polya2005/IoT-RGB-matrix/display_driver/src/gowin_sdpb/gowin_sdpb.v

//Copyright (C)2014-2025 Gowin Semiconductor Corporation.
//All rights reserved.
//File Title: IP file
//Tool Version: V1.9.11.03 Education
//Part Number: GW1NR-LV9QN88PC6/I5
//Device: GW1NR-9
//Device Version: C
//Created Time: Wed Aug 12 21:27:03 2026

module Gowin_SDPB_320_8 (dout, clka, cea, reseta, clkb, ceb, resetb, oce, ada, din, adb);

output [7:0] dout;
input clka;
input cea;
input reseta;
input clkb;
input ceb;
input resetb;
input oce;
input [8:0] ada;
input [7:0] din;
input [8:0] adb;

wire [23:0] sdpb_inst_0_dout_w;
wire gw_gnd;

assign gw_gnd = 1'b0;

SDPB sdpb_inst_0 (
    .DO({sdpb_inst_0_dout_w[23:0],dout[7:0]}),
    .CLKA(clka),
    .CEA(cea),
    .RESETA(reseta),
    .CLKB(clkb),
    .CEB(ceb),
    .RESETB(resetb),
    .OCE(oce),
    .BLKSELA({gw_gnd,gw_gnd,gw_gnd}),
    .BLKSELB({gw_gnd,gw_gnd,gw_gnd}),
    .ADA({gw_gnd,gw_gnd,ada[8:0],gw_gnd,gw_gnd,gw_gnd}),
    .DI({gw_gnd,gw_gnd,gw_gnd,gw_gnd,gw_gnd,gw_gnd,gw_gnd,gw_gnd,gw_gnd,gw_gnd,gw_gnd,gw_gnd,gw_gnd,gw_gnd,gw_gnd,gw_gnd,gw_gnd,gw_gnd,gw_gnd,gw_gnd,gw_gnd,gw_gnd,gw_gnd,gw_gnd,din[7:0]}),
    .ADB({gw_gnd,gw_gnd,adb[8:0],gw_gnd,gw_gnd,gw_gnd})
);

defparam sdpb_inst_0.READ_MODE = 1'b0;
defparam sdpb_inst_0.BIT_WIDTH_0 = 8;
defparam sdpb_inst_0.BIT_WIDTH_1 = 8;
defparam sdpb_inst_0.BLK_SEL_0 = 3'b000;
defparam sdpb_inst_0.BLK_SEL_1 = 3'b000;
defparam sdpb_inst_0.RESET_MODE = "SYNC";

endmodule //Gowin_SDPB_320_8
