polya2005/IoT-RGB-matrix/display_driver/src/bsram_dp/bsram_dp.v

`timescale 1ns/1ps
//Copyright (C)2014-2025 Gowin Semiconductor Corporation.
//All rights reserved.
//File Title: IP file
//Tool Version: V1.9.11.03 Education
//Part Number: GW1NR-LV9QN88PC6/I5
//Device: GW1NR-9
//Device Version: C
//Created Time: Fri Jul 31 19:23:53 2026

module bsram_dp (douta, doutb, clka, ocea, cea, reseta, wrea, clkb, oceb, ceb, resetb, wreb, ada, dina, adb, dinb);

output [7:0] douta;
output [7:0] doutb;
input clka;
input ocea;
input cea;
input reseta;
input wrea;
input clkb;
input oceb;
input ceb;
input resetb;
input wreb;
input [0:0] ada;
input [7:0] dina;
input [0:0] adb;
input [7:0] dinb;

wire [7:0] dpb_inst_0_douta_w;
wire [7:0] dpb_inst_0_doutb_w;
wire gw_gnd;

assign gw_gnd = 1'b0;

DPB dpb_inst_0 (
    .DOA({dpb_inst_0_douta_w[7:0],douta[7:0]}),
    .DOB({dpb_inst_0_doutb_w[7:0],doutb[7:0]}),
    .CLKA(clka),
    .OCEA(ocea),
    .CEA(cea),
    .RESETA(reseta),
    .WREA(wrea),
    .CLKB(clkb),
    .OCEB(oceb),
    .CEB(ceb),
    .RESETB(resetb),
    .WREB(wreb),
    .BLKSELA({gw_gnd,gw_gnd,gw_gnd}),
    .BLKSELB({gw_gnd,gw_gnd,gw_gnd}),
    .ADA({gw_gnd,gw_gnd,gw_gnd,gw_gnd,gw_gnd,gw_gnd,gw_gnd,gw_gnd,gw_gnd,gw_gnd,ada[0],gw_gnd,gw_gnd,gw_gnd}),
    .DIA({gw_gnd,gw_gnd,gw_gnd,gw_gnd,gw_gnd,gw_gnd,gw_gnd,gw_gnd,dina[7:0]}),
    .ADB({gw_gnd,gw_gnd,gw_gnd,gw_gnd,gw_gnd,gw_gnd,gw_gnd,gw_gnd,gw_gnd,gw_gnd,adb[0],gw_gnd,gw_gnd,gw_gnd}),
    .DIB({gw_gnd,gw_gnd,gw_gnd,gw_gnd,gw_gnd,gw_gnd,gw_gnd,gw_gnd,dinb[7:0]})
);

defparam dpb_inst_0.READ_MODE0 = 1'b0;
defparam dpb_inst_0.READ_MODE1 = 1'b0;
defparam dpb_inst_0.WRITE_MODE0 = 2'b00;
defparam dpb_inst_0.WRITE_MODE1 = 2'b00;
defparam dpb_inst_0.BIT_WIDTH_0 = 8;
defparam dpb_inst_0.BIT_WIDTH_1 = 8;
defparam dpb_inst_0.BLK_SEL_0 = 3'b000;
defparam dpb_inst_0.BLK_SEL_1 = 3'b000;
defparam dpb_inst_0.RESET_MODE = "SYNC";

endmodule //bsram_dp
