polya2005/IoT-RGB-matrix/display_driver/src/gowin_sdpb/gowin_sdpb_tmp.v

//Copyright (C)2014-2025 Gowin Semiconductor Corporation.
//All rights reserved.
//File Title: Template file for instantiation
//Tool Version: V1.9.11.03 Education
//Part Number: GW1NR-LV9QN88PC6/I5
//Device: GW1NR-9
//Device Version: C
//Created Time: Wed Aug 12 21:27:03 2026

//Change the instance name and port connections to the signal names
//--------Copy here to design--------

    Gowin_SDPB_320_8 your_instance_name(
        .dout(dout), //output [7:0] dout
        .clka(clka), //input clka
        .cea(cea), //input cea
        .reseta(reseta), //input reseta
        .clkb(clkb), //input clkb
        .ceb(ceb), //input ceb
        .resetb(resetb), //input resetb
        .oce(oce), //input oce
        .ada(ada), //input [8:0] ada
        .din(din), //input [7:0] din
        .adb(adb) //input [8:0] adb
    );

//--------Copy end-------------------
